holmesrichards/dvca/Docs/Layout/dualvca_BackPCB/dualvca_BackPCB_B.Paste.pdf

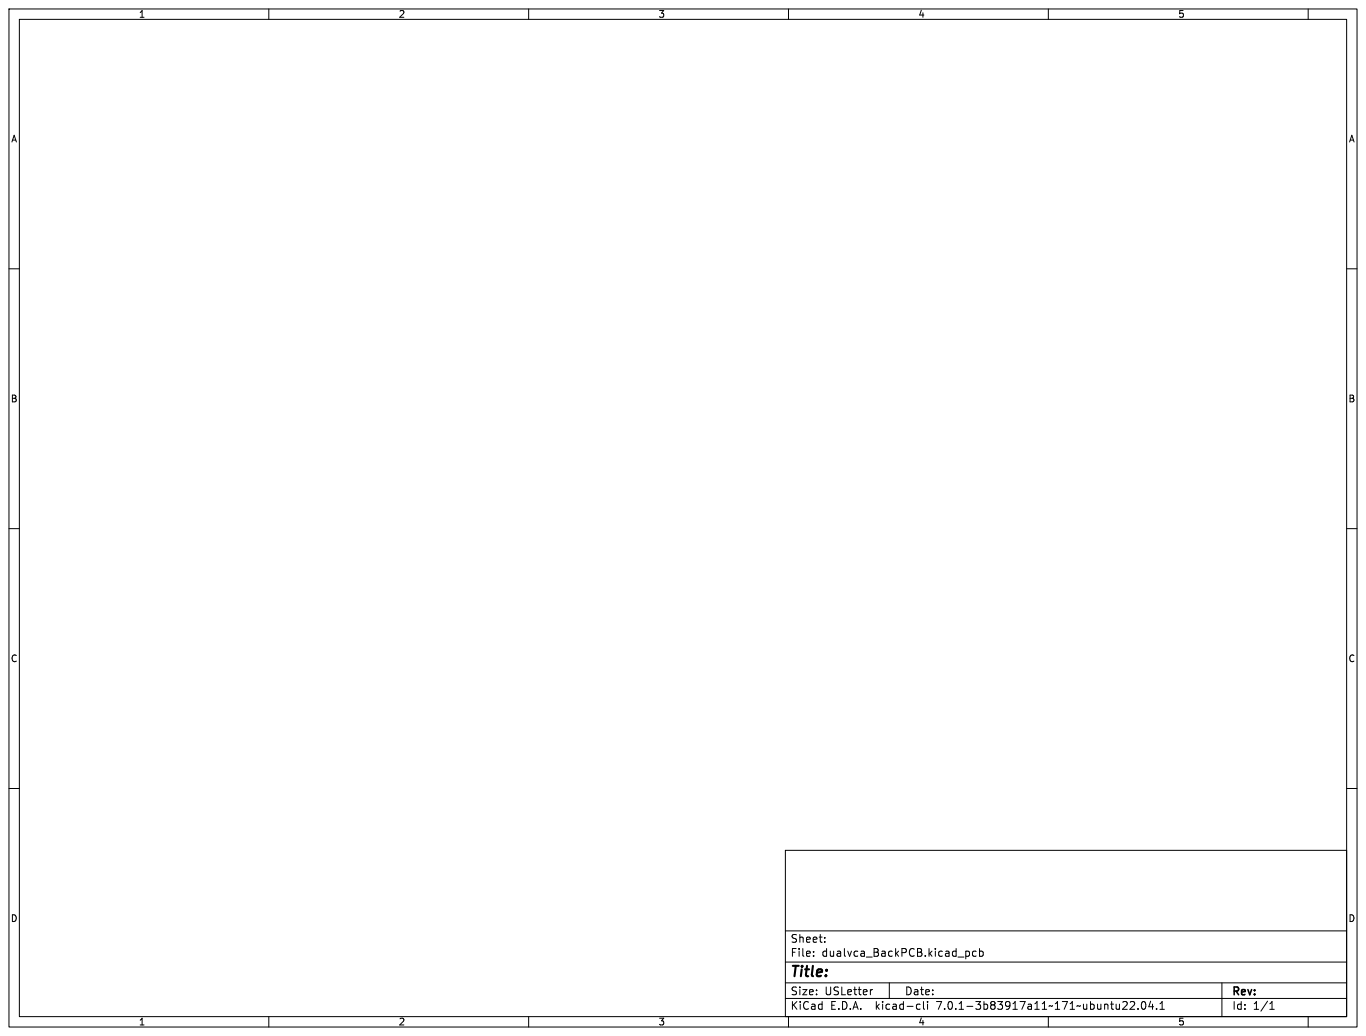
[picture p15: page 1]

Id: 1/1 Title: File: dualvca_BackPCB.kicad_pcb Sheet:
