holmesrichards/dvca/Docs/Layout/dualvca_BackPCB/dualvca_BackPCB_Edge.Cuts.pdf

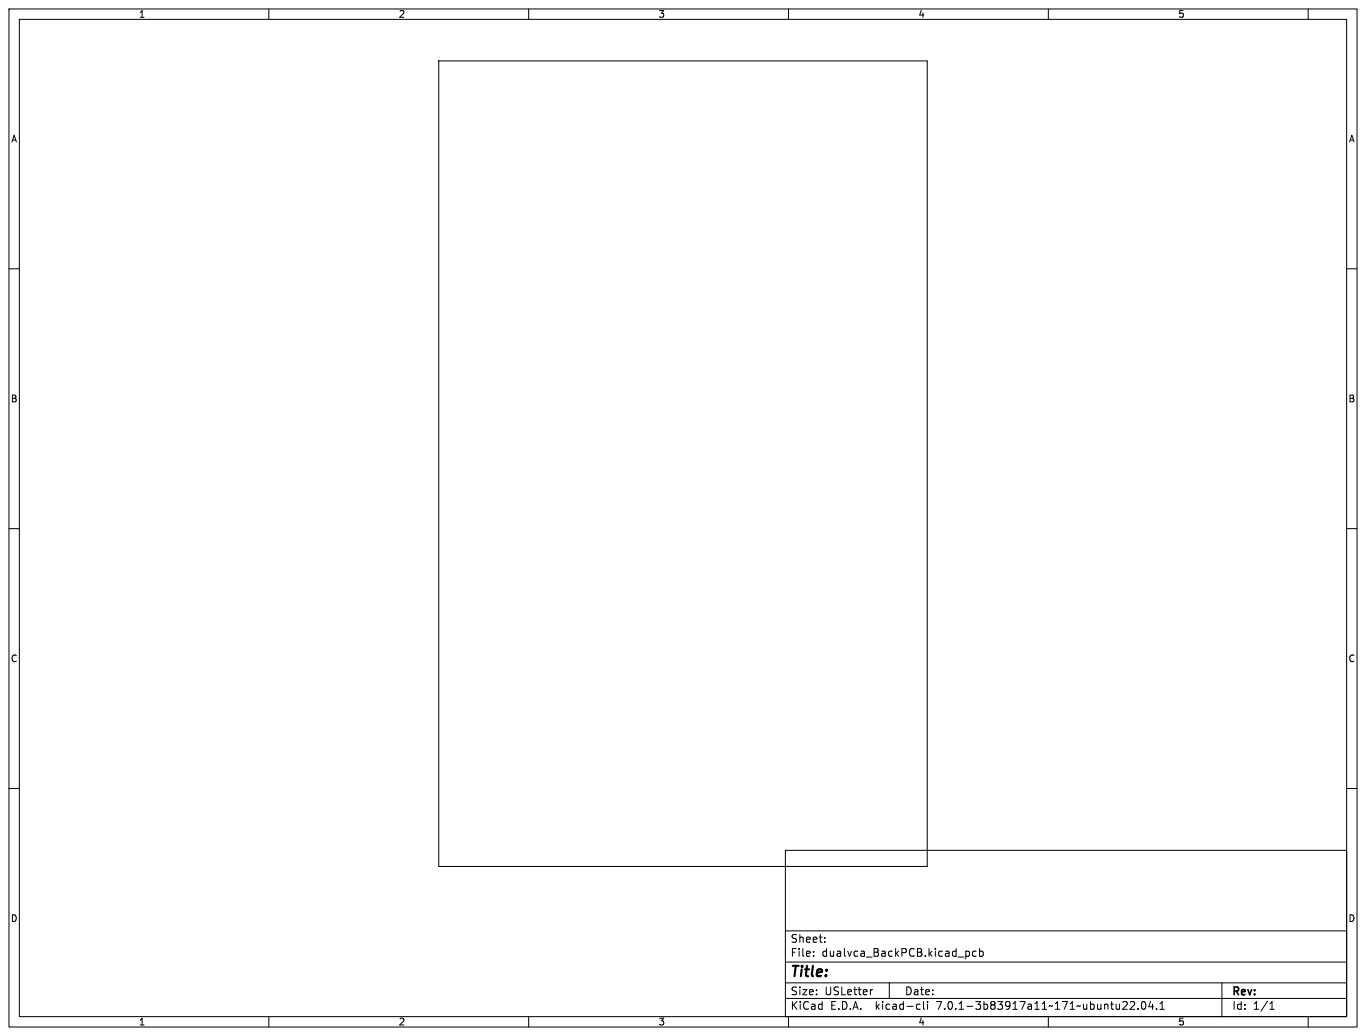
[picture p16: page 1]

Id: 1/1 Title: File: dualvca_BackPCB.kicad_pcb Sheet:
