holmesrichards/dvca/Docs/Layout/dualvca_BackPCB/dualvca_BackPCB_F.Cu.pdf

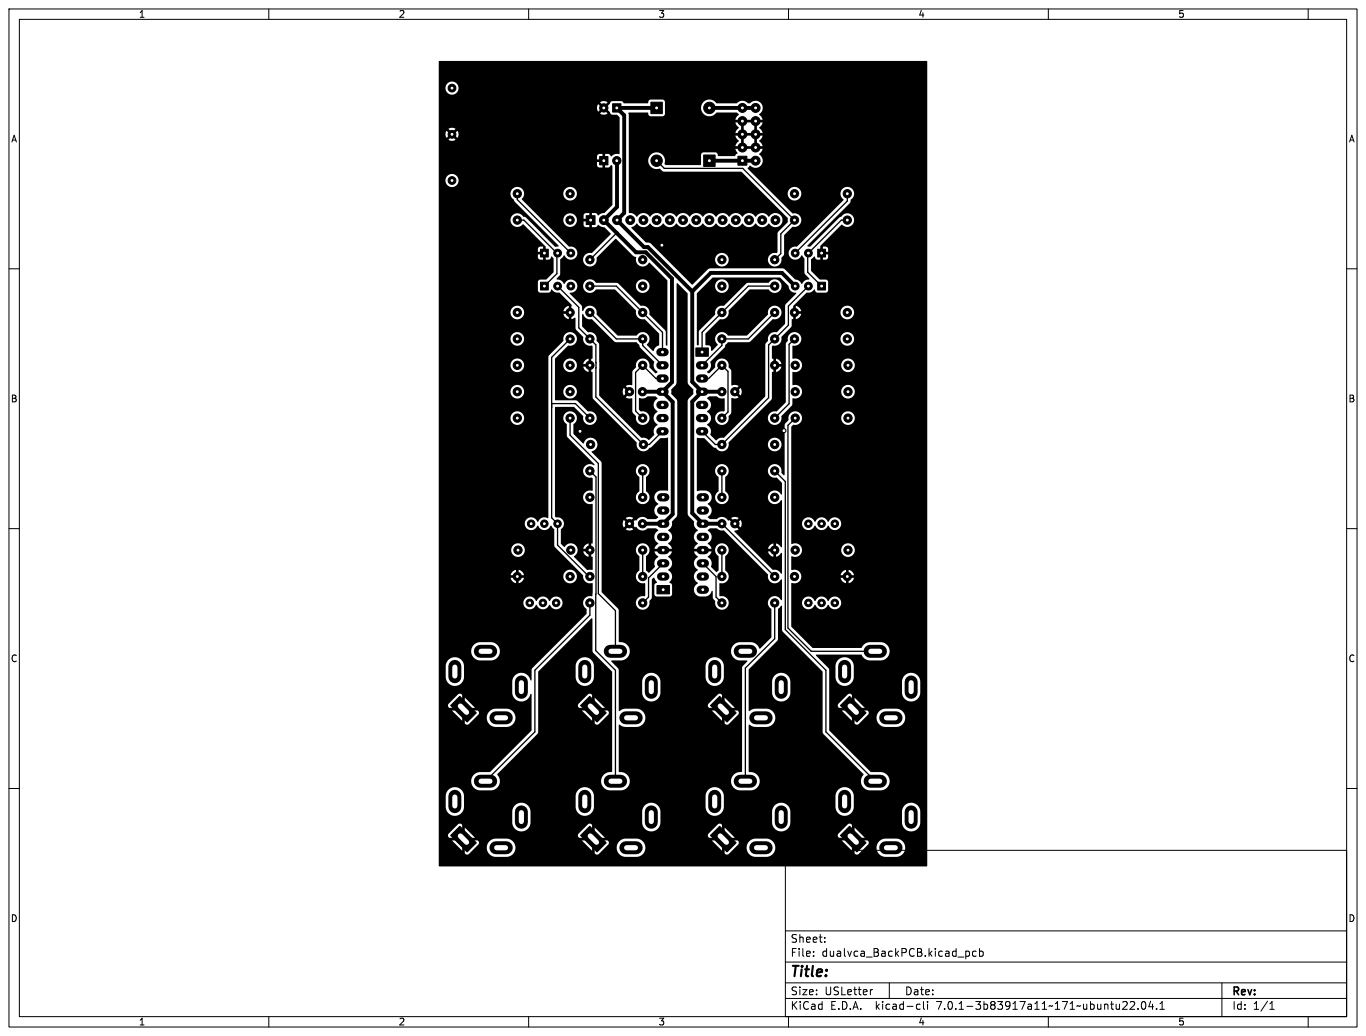
[picture p17: page 1]

Id: 1/1 Title: File: dualvca_BackPCB.kicad_pcb Sheet:
