holmesrichards/dvca/Docs/Layout/dualvca_BackPCB/dualvca_BackPCB_F.Paste.pdf

Id: 1/1 Title: File: dualvca_BackPCB.kicad_pcb Sheet:
