holmesrichards/dvca/Docs/Layout/dualvca_FrontPCB/dualvca_FrontPCB_B.Mask.pdf

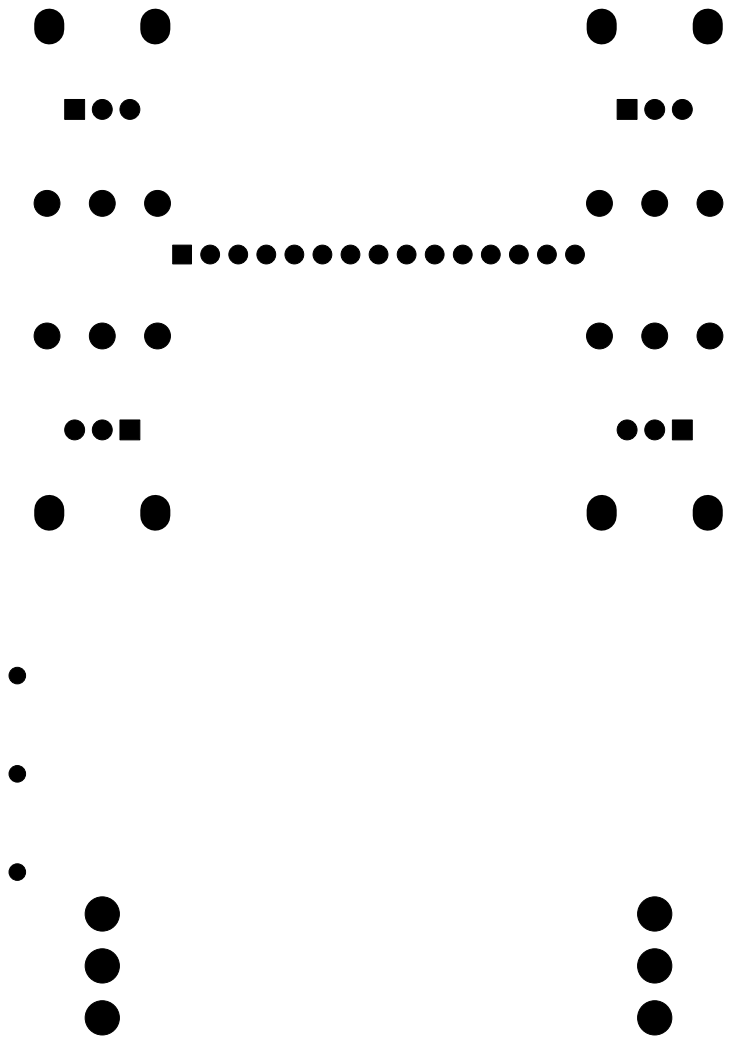
[picture p19: page 1]

Id: 1/1 Title: File: dualvca_FrontPCB.kicad_pcb Sheet:
