holmesrichards/dvca/Docs/Layout/dualvca_FrontPCB/dualvca_FrontPCB_B.Paste.pdf

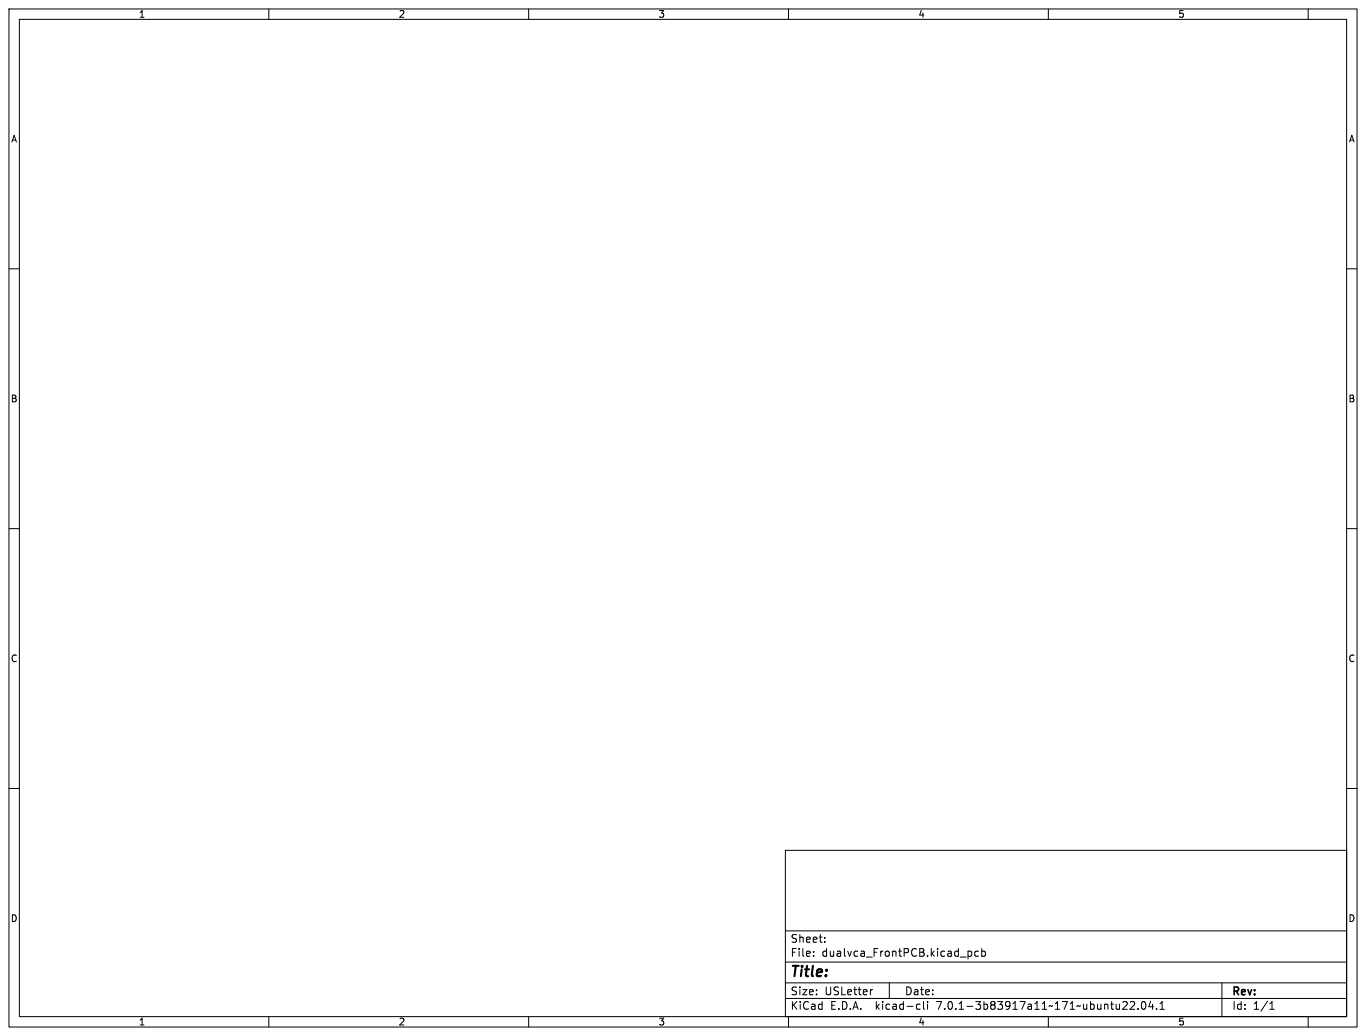
[picture p20: page 1]

Id: 1/1 Title: File: dualvca_FrontPCB.kicad_pcb Sheet:
