holmesrichards/dvca/Docs/Layout/dualvca_FrontPCB/dualvca_FrontPCB_F.Cu.pdf

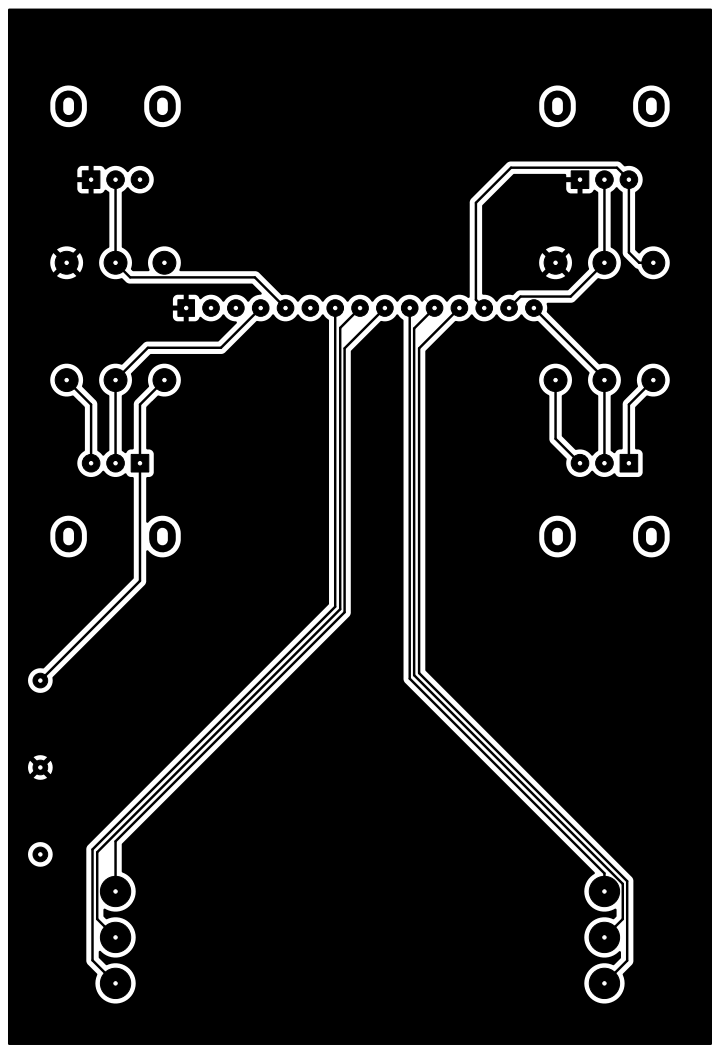
[picture p22: page 1]

Id: 1/1 Title: File: dualvca_FrontPCB.kicad_pcb Sheet:
