holmesrichards/dvca/Docs/Layout/dualvca_FrontPCB/dualvca_FrontPCB_F.Paste.pdf

Id: 1/1 Title: File: dualvca_FrontPCB.kicad_pcb Sheet:
