holmesrichards/dvca/Docs/Layout/dualvca_BackPCB/dualvca_BackPCB_B.SilkS.pdf

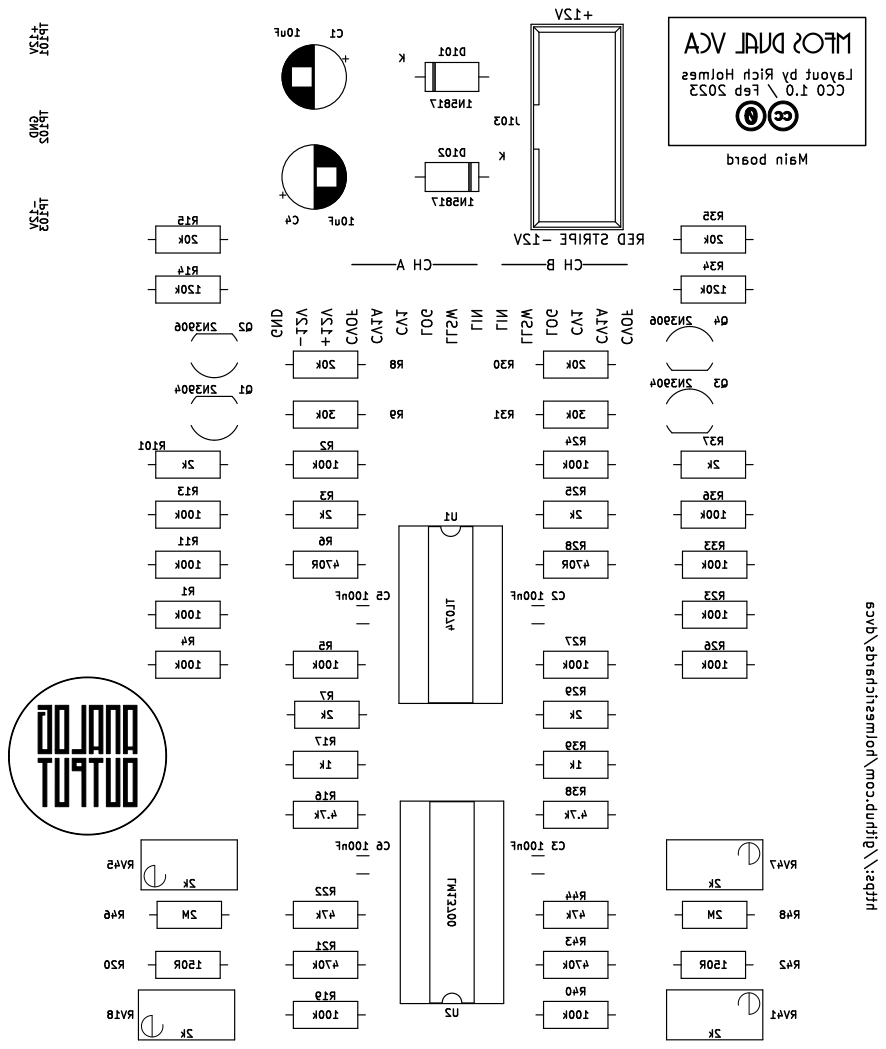
[picture p23: page 1]

MFOSDualVCAhttps://github.com/holmesrichards/dvca CH B
