holmesrichards/dvca/Docs/Layout/dualvca_BackPCB/dualvca_BackPCB_F.SilkS.pdf

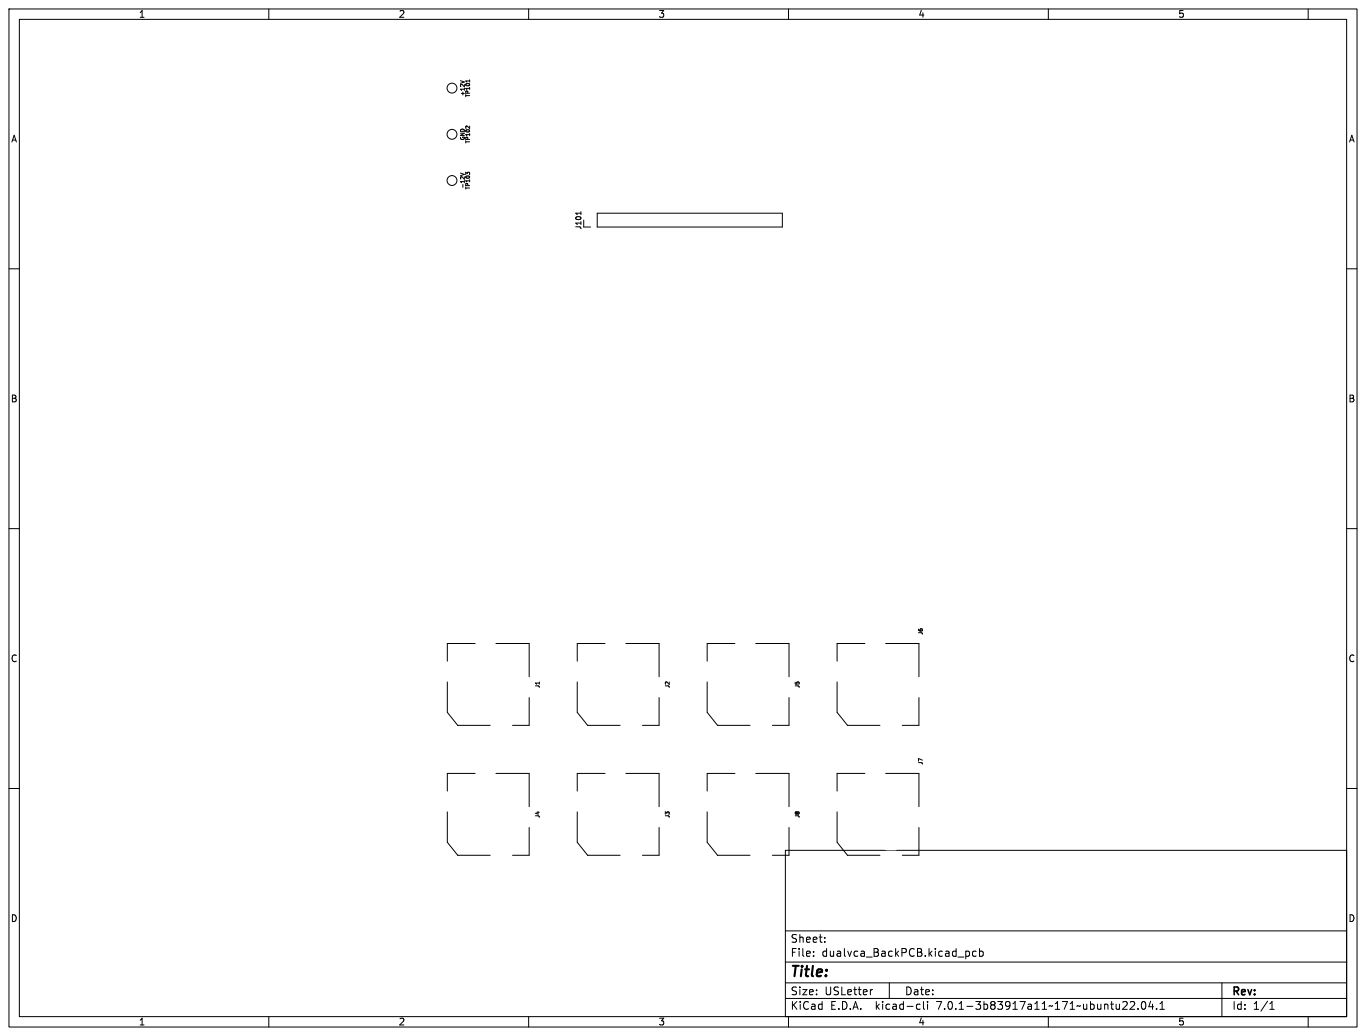
[picture p24: page 1]
