holmesrichards/dvca/Docs/Layout/dualvca_FrontPCB/dualvca_FrontPCB_B.SilkS.pdf

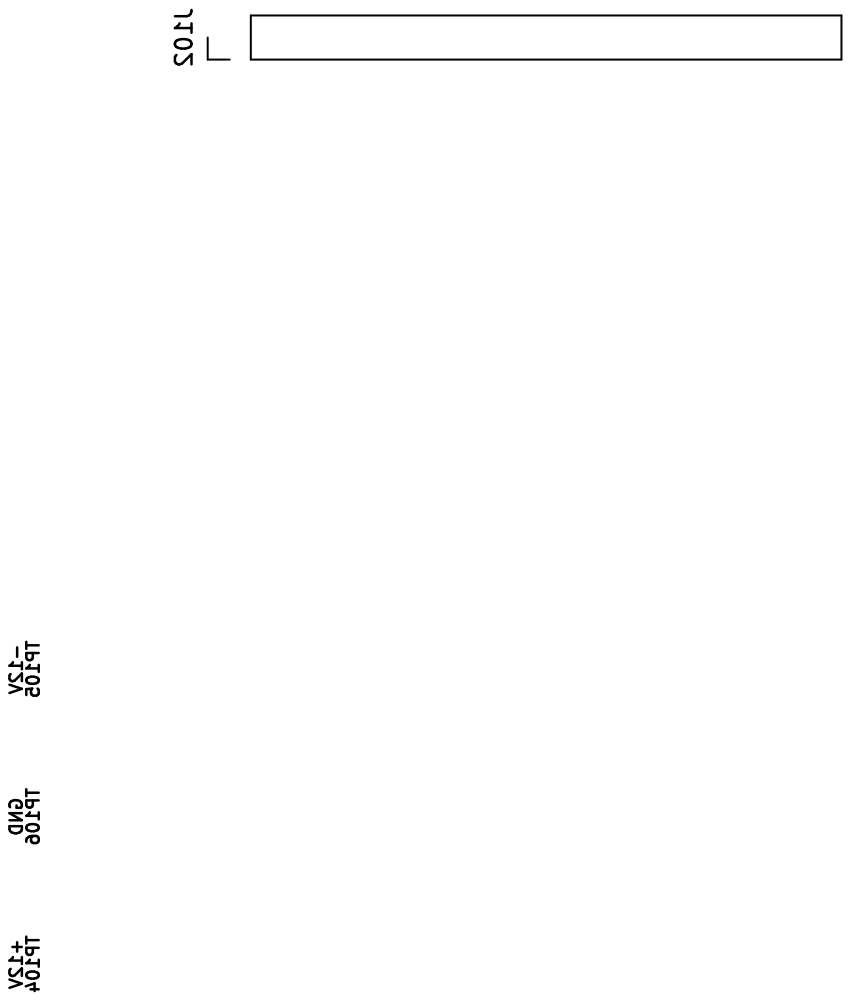
[picture p25: page 1]
