holmesrichards/dvca/Docs/Layout/dualvca_FrontPCB/dualvca_FrontPCB_F.SilkS.pdf

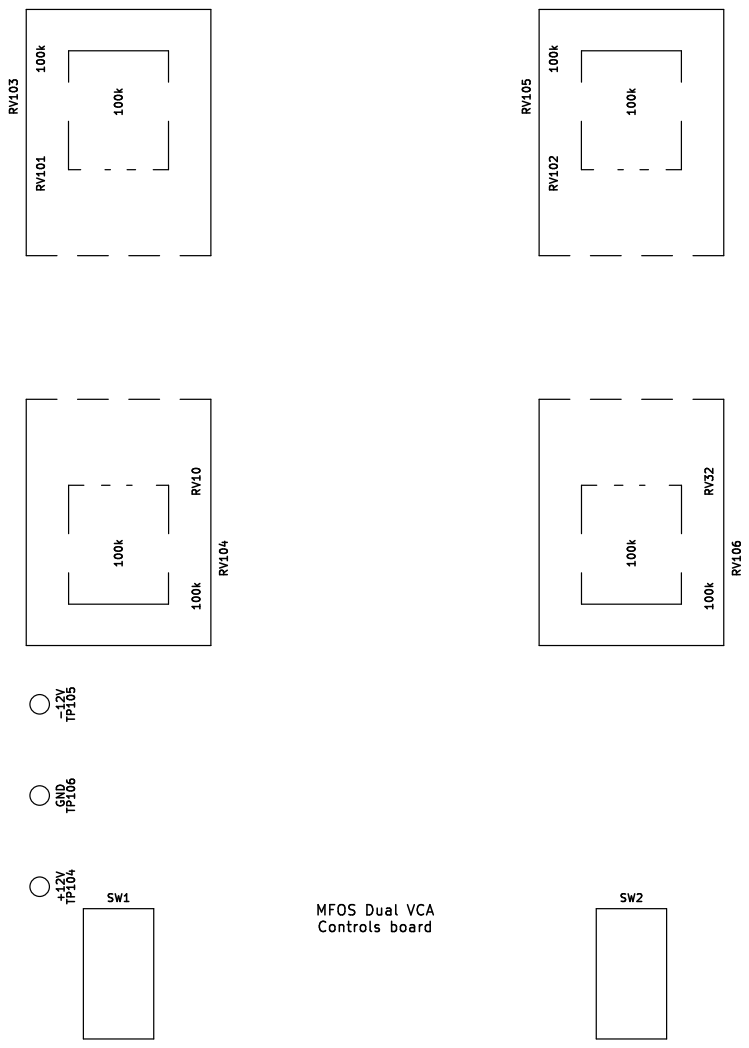
[picture p26: page 1]
